markjhoy/TechWaveAudio-MidiControllerModule/docs/images/mcm-100-small.png

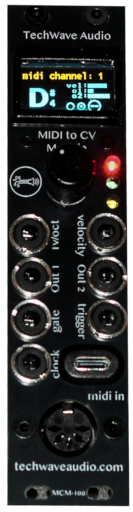
docs/images/mcm-100-small.png
