markjhoy/TechWaveAudio-MidiControllerModule/docs/images/midi_controller_arch.png

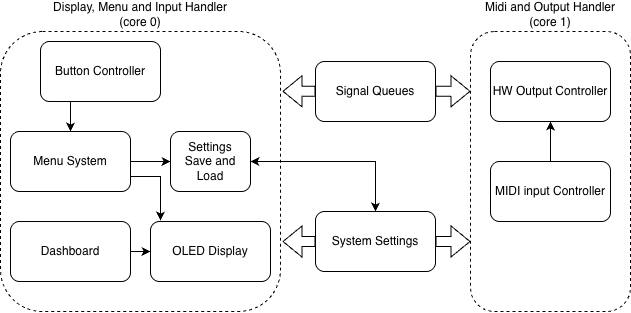
docs/images/midi_controller_arch.png
