markjhoy/TechWaveAudio-MidiControllerModule/src/display/CharacterMapping8x8.h

/*******************************************************************************
 * Copyright (c) 2026 TechWave Audio (techwaveaudio.com)
 *
 * SPDX-License-Identifier: BSD-3-Clause
 *
 ******************************************************************************/

#ifndef TECHWAVEAUDIO_MCM_CHARACTERMAPPING8X8_H
#define TECHWAVEAUDIO_MCM_CHARACTERMAPPING8X8_H
#include "BaseCharacterSet.h"

/**
 * A basic 8x8 character set
 */
class CharacterMapping8x8 : public BaseCharacterSet {
public:
    CharacterMapping8x8();
};

#define CHAR_MAPPING_BYTE_WIDTH_8x8_FONT 8
#define CHAR_MAPPING_BYTE_HEIGHT_8x8_FONT 8
#define CHAR_MAPPING_BYTE_SIZE_8x8_FONT (BASE_CHARACTER_SET_NUM_CHARS_DEFINED * CHAR_MAPPING_BYTE_WIDTH_8x8_FONT * CHAR_MAPPING_BYTE_HEIGHT_8x8_FONT)

static uint8_t char_byte_mapping_8x8[CHAR_MAPPING_BYTE_SIZE_8x8_FONT] = {
    0b00000000,
  0b00000000,
  0b00000000,
  0b00000000,
  0b00000000,
  0b00000000,
  0b00000000,
  0b00000000,
    0b00011000,
  0b00011000,
  0b00011000,
  0b00011000,
  0b00011000,
  0b00000000,
  0b00011000,
  0b00000000,
    0b01100110,
  0b01000100,
  0b01000100,
  0b00100010,
  0b00000000,
  0b00000000,
  0b00000000,
  0b00000000,
    0b00000000,
  0b00010100,
  0b00111110,
  0b00010100,
  0b00111110,
  0b00010100,
  0b00000000,
  0b00000000,
    0b00001000,
  0b00111100,
  0b00001010,
  0b00011100,
  0b00101000,
  0b00011110,
  0b00001000,
  0b00000000,
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
};


#endif //TECHWAVEAUDIO_MCM_CHARACTERMAPPING8X8_H
