markjhoy/TechWaveAudio-MidiControllerModule/src/Controller.cpp

/*******************************************************************************
 * Copyright (c) 2026 TechWave Audio (techwaveaudio.com)
 *
 * SPDX-License-Identifier: BSD-3-Clause
 *
 ******************************************************************************/

#include "./TechWaveAudio_MidiControllerModule.h"
#include "Controller.h"
#include "GlobalHandlers.h"

#include <cmath>

#include "TestingMenuSystemHandler.h"
#include "tusb.h"
#include "tusb_config.h"
#include "common/tusb_types.h"
#include "hardware/PowerSystem.h"
#include "menu/TestingMenu.h"
#include "pico/multicore.h"

#define MIDI_NOTE_VALUE_MIDDLE_A 69.0
#define NOTE_FREQUENCY_MIDDLE_A 440.0
#define NOTE_FREQUENCY_C6 1046.50

void initialize_dac_lookup_tables() {
    float linearStepSize12Bit10v = 4096.0f / MAX_NUM_NOTES_10V;
    for (int i = 0; i < MAX_NUM_NOTES_10V; i++) {
        ten_volt_note_12_bit_output[i] = static_cast<uint16_t>(static_cast<float>(i) * linearStepSize12Bit10v);
    }

    float linearStepSize12Bit5v = 4096.0f / MAX_NUM_NOTES_5V;
    for (int i = 0; i < MAX_NUM_NOTES_5V; i++) {
        five_volt_note_12_bit_output[i] = static_cast<uint16_t>(static_cast<float>(i) * linearStepSize12Bit5v);
    }

    float linearStepSize12BitsLinear = 4096.0f / MAX_MIDI_DATA_VALUE;
    for (int i = 0; i < MAX_MIDI_DATA_VALUE; i++) {
        ten_volt_linear_12_bit_output[i] = static_cast<uint16_t>(static_cast<float>(i) * linearStepSize12BitsLinear);
    }
}

void diagnosticMessage(OledDisplay *display, const std::string &message) {
#ifdef DISPLAY_BOOT_DIAGNOSTICS
    display->clear(true);
    display->writeTextStartingAtLine(0, message);
    display->show();
#endif
}

/**
 * Our main core 1 launcher for midi and output handling
 */
void launch_midi_and_output_handler() {
    if (get_core_num() == 0) {
        // only run on core 1
        return;
    }

    tusb_rhport_init_t host_init = {
        .role = TUSB_ROLE_DEVICE,
        .speed = TUSB_SPEED_AUTO
    };
    tusb_init(BOARD_TUD_RHPORT, &host_init);

    global_midi_output_handler->init();

    while (global_midi_output_handler->shouldKeepRunning()) {
        tud_task();
        global_midi_output_handler->processEvents();
    }
}

Controller::Controller() {
    gpio_set_function(OLED_I2C_DATA_PIN, GPIO_FUNC_I2C);
    gpio_set_function(OLED_I2C_CLOCK_PIN, GPIO_FUNC_I2C);
    gpio_pull_up(OLED_I2C_DATA_PIN);
    gpio_pull_up(OLED_I2C_CLOCK_PIN);
}

Controller::~Controller() {
    shutdown();

    delete _menuSystem;
    delete _lcdDisplay;
    delete _encoder;
    delete _timerQueue;

    delete _lcdI2c;
}

void Controller::run() {
    // ensure we're on core 0
    if (get_core_num() != 0) {
        return;
    }

    gpio_put(PIN_NOTE_LED, true);
    gpio_put(PIN_CLOCK_LED, true);

    global_system_state->expansionSensed = SettingsMenuSystem::senseExpansion();

    initHardware();

    // ensure that USB is not plugged in
    bool isVSysPower = false;
    PowerSystem::getPowerSource(&isVSysPower);
    if (!isVSysPower) {
        // if we have USB power - do not start up
        _lcdDisplay->clear(true);
        _lcdDisplay->writeLineAt(1, "   Unplug USB", false);
        _lcdDisplay->show();
        gpio_put(PIN_NOTE_LED, false);
        gpio_put(PIN_CLOCK_LED, false);

        // and wait until we do not have USB power
        while (!isVSysPower) {
            PowerSystem::getPowerSource(&isVSysPower);
            tight_loop_contents();
        }

        _lcdDisplay->clear(true);
    }

    // display the boot screen
    showBootSequence();

    diagnosticMessage(_lcdDisplay, "completed boot sequence");

    initialize_dac_lookup_tables();

    diagnosticMessage(_lcdDisplay, "completed DAC tables init");

    // load persisted state and set menu handlers
    _menuSystem->loadState();
    diagnosticMessage(_lcdDisplay, "loaded settings state");

    _menuSystem->setOnEnteringMenu([this] { this->onEnterMenu(); });
    _menuSystem->setOnExitingMenu([this] { this->onExitMenu(); });

    diagnosticMessage(_lcdDisplay, "completed menu init");

    global_core0_handler->init();
    diagnosticMessage(_lcdDisplay, "completed core0 init");

    global_core0_handler->setMenuSystem(_menuSystem);
    diagnosticMessage(_lcdDisplay, "completed core0 setMenuSystem");

    multicore_reset_core1();
    TimedEventQueue::nonBlockingWait(50);
    multicore_launch_core1(&launch_midi_and_output_handler);

    diagnosticMessage(_lcdDisplay, "completed core1 launch");

    // and turn off the boot screen
    completeBootSequence();

    // if we're holding down the encoder button
    // go into the diagnostic / test (calibration) menu
    bool encButtonState = gpio_get(ENC_BUTTON_PIN);
    if (encButtonState) {
        showTestMenu();
    }

    // set our dashboard display
    _menuSystem->changeMenu(nullptr);

    TimedEventQueue::nonBlockingWait(100);

    // signal to start our output controller on core 1
    global_core0_handler->turnOnGlobalOutputController();

    // 2 seconds w/out a message
    auto midiSenseExpiration = make_timeout_time_ms(2000);

    // main loop
    while (!_menuSystem->shouldExit()) {
        auto now = make_timeout_time_ms(0);

        // process any signals from core 1
        bool eventWasProcessed = global_core0_handler->processEvents();

        if (eventWasProcessed)
            // 2 seconds w/out a message
            midiSenseExpiration = make_timeout_time_ms(2000);

        // process any events in the timer queue
        _timerQueue->pollAndProcessEvents();

        // if we're in a menu, don't update the dashboard
        if (_menuSystem->isInMenu()) {
            continue;
        }

        bool midiSensed = (absolute_time_diff_us(now, midiSenseExpiration)) > 0;

        // update the dashboard
        _menuSystem->updateDashboard(midiSensed);
    }
    global_core0_handler->shutdown();
}

void Controller::shutdown() const {
    _encoder->shutdown();
    _menuSystem->shutdown();
    _timerQueue->clear();
    _lcdDisplay->clear();
}

void Controller::initHardware() {
    _timerQueue = new TimedEventQueue();
    _encoder = new RotaryEncoder(_timerQueue, ENC_RIGHT_PIN, ENC_LEFT_PIN, ENC_BUTTON_PIN);

    _lcdI2c = new HardwareI2C(&HW_OLED_I2C, OLED_I2C_DATA_PIN, OLED_I2C_CLOCK_PIN, OLED_BUS_HARDWARE_FREQ);
    _lcdDisplay = new OledDisplay(_lcdI2c);

    _menuSystem = new SettingsMenuSystem(_lcdDisplay, _timerQueue, _encoder);
}

void Controller::enterMenuButtonPressed() const {
    _menuSystem->showMainMenu();
}

void Controller::onEnterMenu() {
    _initialState = (*global_system_state);
}

void Controller::onExitMenu() {
    _encoder->setOnLeftTurn(nullptr);
    _encoder->setOnRightTurn(nullptr);
    _encoder->setOnPressed([this] { this->enterMenuButtonPressed(); });
    if (_menuSystem->didStateChange(_initialState)) {
        _menuSystem->saveState();
    }
    _initialState = (*global_system_state);
}

void Controller::showBootSequence() {
    _lcdDisplay->displayBootScreen();
}

void Controller::completeBootSequence() {
    // sanity check with a light pattern to ensure we know
    // we've booted correctly
    TimedEventQueue::nonBlockingWait(500);
    gpio_put(PIN_NOTE_LED, false);
    gpio_put(PIN_CLOCK_LED, false);
    TimedEventQueue::nonBlockingWait(250);
    gpio_put(PIN_NOTE_LED, true);
    TimedEventQueue::nonBlockingWait(250);
    gpio_put(PIN_CLOCK_LED, true);
    TimedEventQueue::nonBlockingWait(250);
    gpio_put(PIN_NOTE_LED, false);
    TimedEventQueue::nonBlockingWait(250);
    gpio_put(PIN_CLOCK_LED, false);
}

void Controller::showTestMenu() const {
    auto testingMenuSystem = new TestingMenuSystemHandler(_lcdDisplay, _timerQueue, _encoder);
    auto testMenu = new TestingMenu(_lcdDisplay, testingMenuSystem, global_system_state, nullptr, _encoder);

    testingMenuSystem->changeMenu(testMenu);
    TimedEventQueue::nonBlockingWait(100);

    while (!testingMenuSystem->shouldExit()) {
        global_core0_handler->processEvents();
        _timerQueue->pollAndProcessEvents();
    }

    delete testMenu;
    delete testingMenuSystem;
}
