markjhoy/TechWaveAudio-MidiControllerModule/src/hardware/RotaryEncoder.h

/*******************************************************************************
 * Copyright (c) 2026 TechWave Audio (techwaveaudio.com)
 *
 * SPDX-License-Identifier: BSD-3-Clause
 *
 ******************************************************************************/

#ifndef TECHWAVEAUDIO_MCM_ROTARTYENCODER_H
#define TECHWAVEAUDIO_MCM_ROTARTYENCODER_H

#include "GpioPinEventHandler.h"
#include "../TechWaveAudio_MidiControllerModule.h"
#include "../common/TimedEventQueue.h"

enum RotaryEncoderSequenceStart : uint8_t {
    RotaryEncoderSequenceStart_None = 0,
    RotaryEncoderSequenceStart_PinA = 0b00000010,
    RotaryEncoderSequenceStart_PinB = 0b00000001,
};

/**
 * A rotary encoder handler with push button functionality
 */
class RotaryEncoder {
public:
    RotaryEncoder(TimedEventQueue *timedEventQueue, uint8_t pinA, uint8_t pinB, uint8_t buttonPin);
    ~RotaryEncoder();

    /**
     * Sets the function to callback when the encoder is turned left 1 position
     * @param callback the callback function
     */
    void setOnLeftTurn(const GeneralFunctionCallback &callback);

    /**
     * Sets the function to callback when the encoder is turned right 1 position
     * @param callback the callback function
     */
    void setOnRightTurn(const GeneralFunctionCallback &callback);

    /**
     * Sets the function to callback when the button is pressed
     * @param callback the callback function
     */
    void setOnPressed(const GeneralFunctionCallback &callback);

    /**
     * Sets the function to callback when the button is released
     * @param callback the callback function
     */
    void setOnReleased(const GeneralFunctionCallback &callback);

    /**
     * Called on system shutdown
     */
    void shutdown();

private:
    TimedEventQueue *_timedEventQueue = nullptr;
    uint8_t _pinA = 0;
    uint8_t _pinB = 0;
    uint8_t _buttonPin = 0;

    int _state = 0b00000011;
    int _stateSum = 0;
    int STATE_MAP[16] =  {0, -1, 1, 14, 1, 0, 14, -1, -1, 14, 0, 1, 14, 1, -1, 0};

    GpioPinEventHandler *_leftPinEventHandler = nullptr;
    GpioPinEventHandler *_rightPinEventHandler = nullptr;
    GpioPinEventHandler *_buttonEventHandler = nullptr;

    GeneralFunctionCallback _onLeftTurnCallback = nullptr;
    GeneralFunctionCallback _onRightTurnCallback = nullptr;
    GeneralFunctionCallback _onPressedCallback = nullptr;
    GeneralFunctionCallback _onReleasedCallback = nullptr;

    void setupDevice();
    void onEncoderDirectionChangeCallback(uint8_t pin, bool value);
    void onButtonPressedCallback(uint8_t pin, bool value);
};


#endif //TECHWAVEAUDIO_MCM_ROTARTYENCODER_H
