markjhoy/TechWaveAudio-MidiControllerModule/src/Controller.h

/*******************************************************************************
 * Copyright (c) 2026 TechWave Audio (techwaveaudio.com)
 *
 * SPDX-License-Identifier: BSD-3-Clause
 *
 ******************************************************************************/

#ifndef TECHWAVEAUDIO_MIDI_CONTROLLER_MODULE_CONTROLLER_H
#define TECHWAVEAUDIO_MIDI_CONTROLLER_MODULE_CONTROLLER_H

#include "common/TimedEventQueue.h"
#include "display/OledDisplay.h"
#include "SettingsMenuSystem.h"

/**
 * Primary controller for the application.
 * Handles running the main loop, event handling, and shutdown
 */
class Controller {
public:
    Controller();
    ~Controller();

    /**
     * Run the main loop
     */
    void run();

    /**
     * Call this to shut down all processes.
     * Should be called after the main loop has exited.
     */
    void shutdown() const;

private:
    HardwareI2C *_lcdI2c = nullptr;
    OledDisplay *_lcdDisplay = nullptr;
    TimedEventQueue *_timerQueue = nullptr;
    RotaryEncoder * _encoder = nullptr;
    SettingsMenuSystem *_menuSystem = nullptr;
    SystemState _initialState;

    void initHardware();
    void enterMenuButtonPressed() const;
    void onEnterMenu();
    void onExitMenu();
    void showBootSequence();
    static void completeBootSequence();

    void showTestMenu() const;
};

#endif // TECHWAVEAUDIO_MIDI_CONTROLLER_MODULE_CONTROLLER_H
