markjhoy/TechWaveAudio-MidiControllerModule/src/io/MidiAndOutputHandler.cpp

/*******************************************************************************
 * Copyright (c) 2026 TechWave Audio (techwaveaudio.com)
 *
 * SPDX-License-Identifier: BSD-3-Clause
 *
 ******************************************************************************/

#include "../GlobalHandlers.h"

MidiAndOutputHandler::MidiAndOutputHandler(queue_t *inputQueue, queue_t *outputQueue)
: CoreHandler(inputQueue, outputQueue) {
    _keepRunning = true;
    _eventQueue = new TimedEventQueue();
    _outputController = new OutputController(global_system_state, _eventQueue, this->getMultiCoreController());
}

MidiAndOutputHandler::~MidiAndOutputHandler() {
    delete _outputController;
    delete _eventQueue;
}

bool MidiAndOutputHandler::processSignalMessage(SignalCommand command, uint8_t data) {
    switch (command) {
        case SignalCommand_OutputOn: {
            _outputController->init();
        } break;
        case SignalCommand_OutputOff: {
            _outputController->shutdown();
        } break;
        case SignalCommand_UpdateMappings: {
            _outputController->updateMappingRoutes();
        } break;
        case SignalCommand_Shutdown: {
            _outputController->shutdown();
            this->_keepRunning = false;
            this->sendSignal(SignalCommand_Shutdown_Ack, 0);
        } break;
        default: {
            return false;
        }
    }
    return true;
}

void MidiAndOutputHandler::onAfterProcessEvents(bool messagesProcessed) {
    _outputController->processMidiQueue();
    _eventQueue->pollAndProcessEvents();
}
