markjhoy/TechWaveAudio-MidiControllerModule/src/hardware/Mcp4725.cpp

/*******************************************************************************
 * Copyright (c) 2026 TechWave Audio (techwaveaudio.com)
 *
 * SPDX-License-Identifier: BSD-3-Clause
 *
 ******************************************************************************/

#include "Mcp4725.h"

Mcp4725::Mcp4725(HardwareI2C *i2c, int8_t address) {
    _i2c = i2c;
    _address = address;
    write(0);
}

void Mcp4725::write(int value) {
    auto valueToWrite = static_cast<uint16_t>(value);
    if (value < 0) {
        valueToWrite = 0;
    } else if (value > 4095) {
        valueToWrite = 4095;
    }

    _buffer[0] = 0x00 | ((valueToWrite >> 8) & 0x0F);
    _buffer[1] = valueToWrite & 0xFF;
    _i2c->write(_address, _buffer, 2);
}
